TaISLab/Dummy-Arm/CAD/joint3A2.SLDPRT

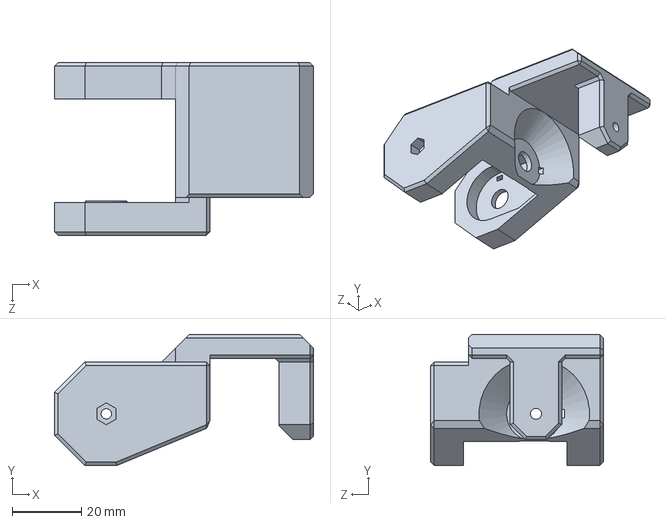
[picture p21: CAD file, 2023-08-25]
CAD/joint3A2.SLDPRT
75.0 x 38.0 x 50.0 mm
