TaISLab/Dummy-Arm/CAD/humero3.SLDPRT

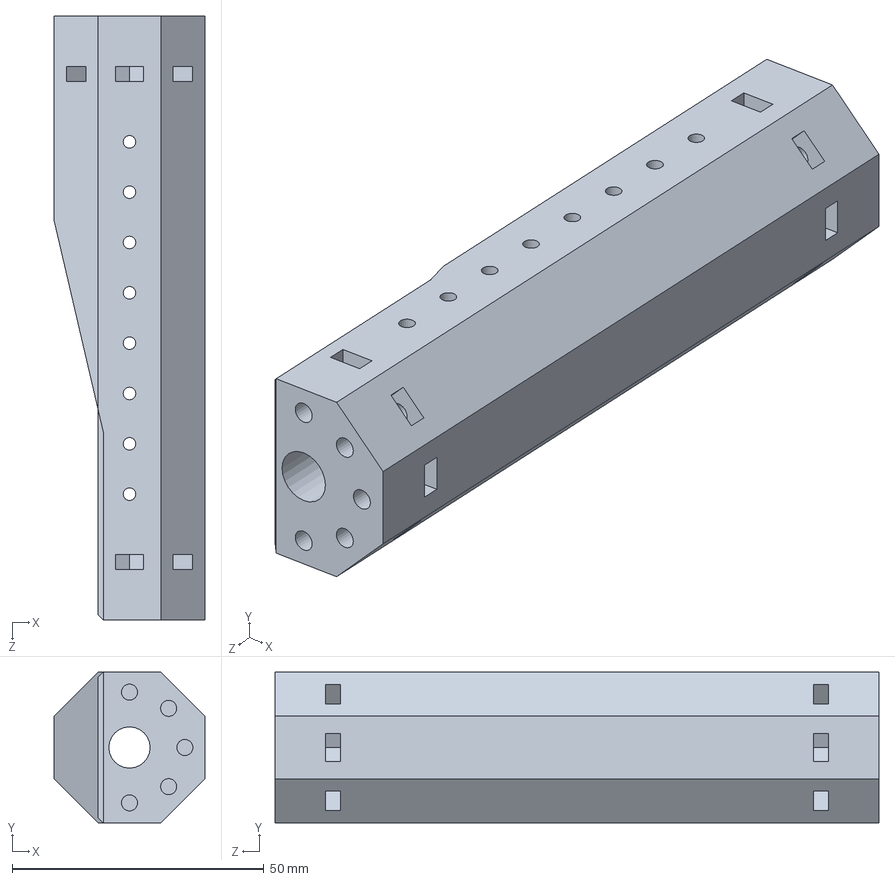
[picture p22: CAD file, 2023-08-25]
CAD/humero3.SLDPRT
30.0 x 30.0 x 120.0 mm
