TaISLab/Dummy-Arm/CAD/jointB.SLDPRT

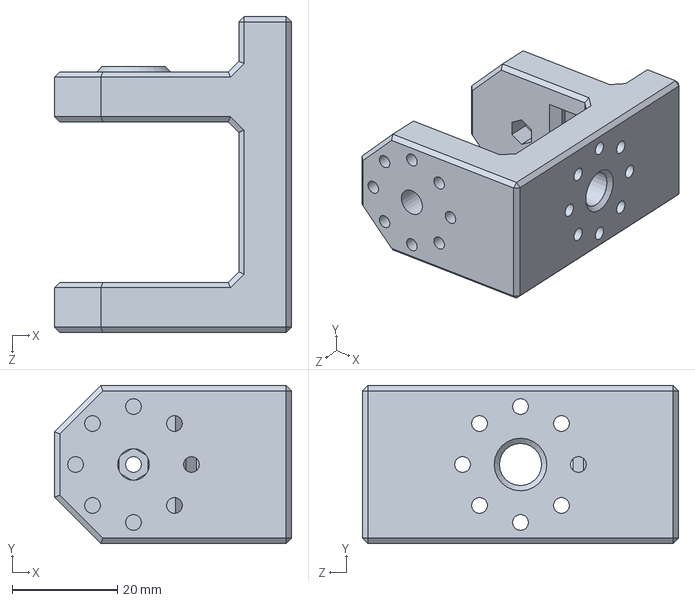
[picture p23: CAD file, 2023-08-25]
CAD/jointB.SLDPRT
45.0 x 30.0 x 60.0 mm
