TaISLab/Dummy-Arm/CAD/wrist.SLDPRT

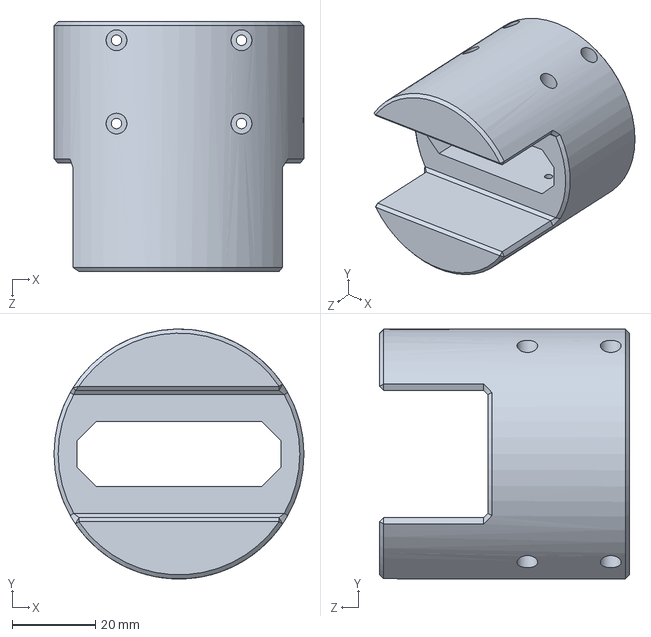
[picture p24: CAD file, 2023-08-25]
CAD/wrist.SLDPRT
60.0 x 60.0 x 60.0 mm
