TaISLab/Dummy-Arm/CAD/radius-ulna3.SLDPRT

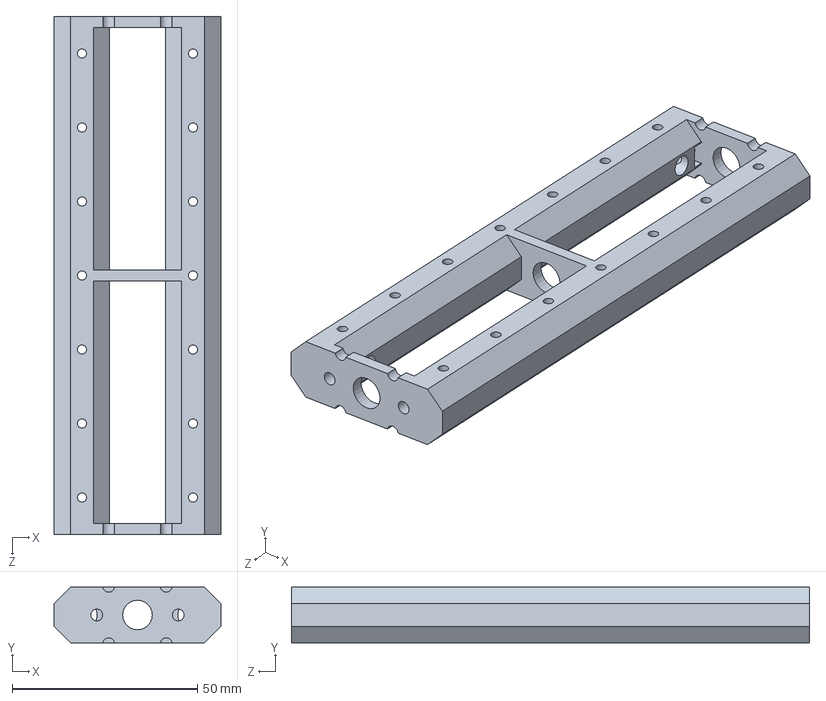
[picture p25: CAD file, 2023-08-25]
CAD/radius-ulna3.SLDPRT
45.0 x 15.0 x 140.0 mm
