TaISLab/Dummy-Arm/CAD/jointA.SLDPRT

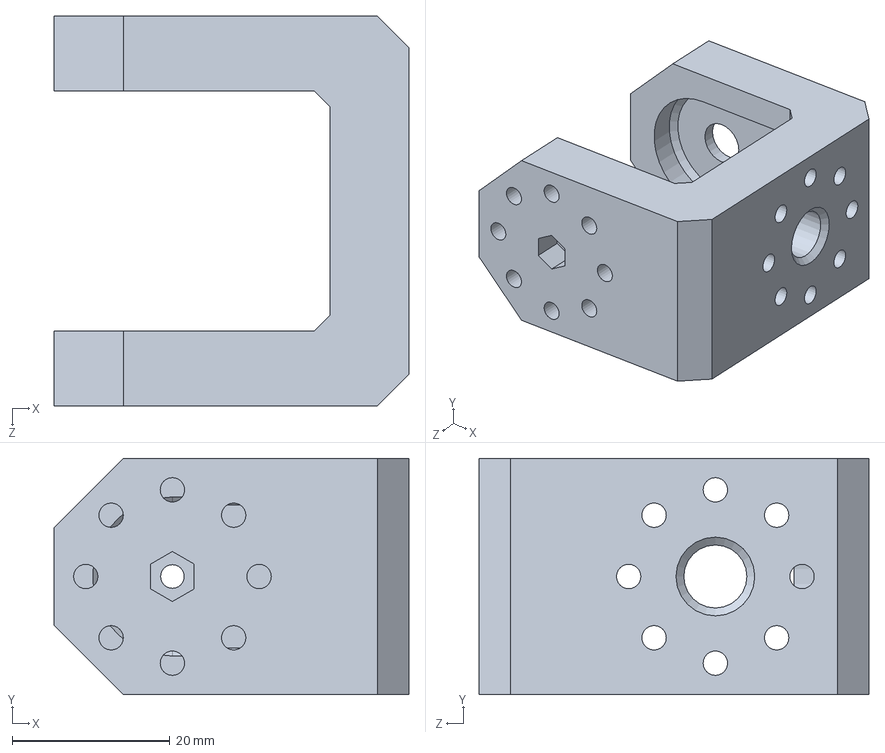
[picture p26: CAD file, 2023-08-25]
CAD/jointA.SLDPRT
45.0 x 30.0 x 49.5 mm
