TaISLab/Dummy-Arm/CAD/humeroB.SLDPRT

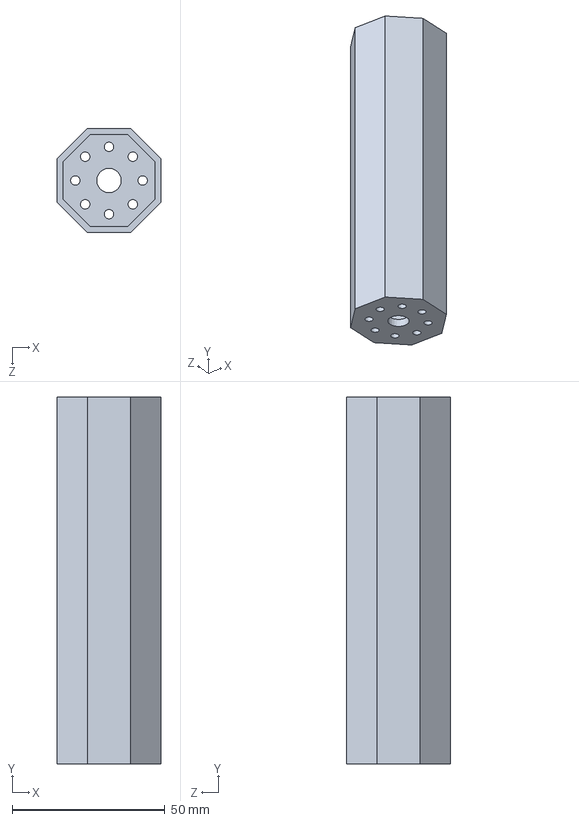
[picture p27: CAD file, 2023-08-24]
CAD/humeroB.SLDPRT
34.0 x 120.0 x 34.0 mm
