TaISLab/Dummy-Arm/CAD/humeroXA.SLDPRT

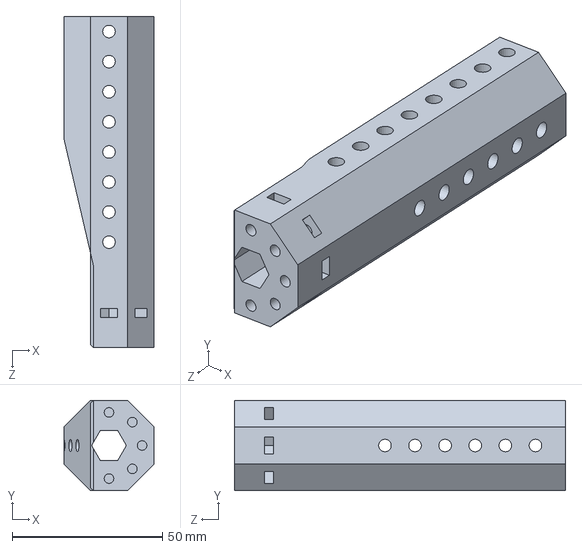
[picture p28: CAD file, 2023-08-24]
CAD/humeroXA.SLDPRT
30.0 x 30.0 x 110.0 mm
