TaISLab/Dummy-Arm/CAD/humero2.SLDPRT

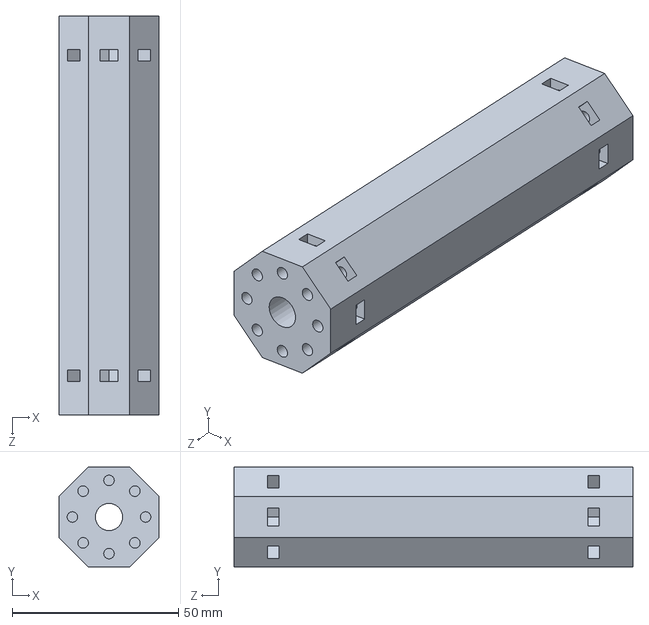
[picture p29: CAD file, 2023-08-24]
CAD/humero2.SLDPRT
30.0 x 30.0 x 120.0 mm
