TaISLab/Dummy-Arm/CAD/humeroA.SLDPRT

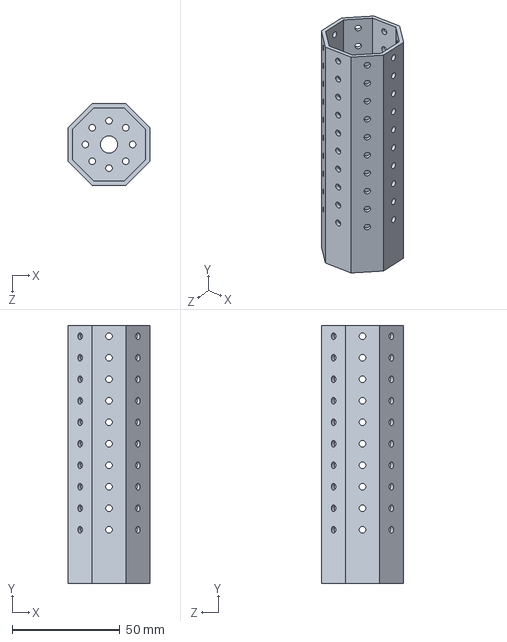
[picture p30: CAD file, 2023-08-24]
CAD/humeroA.SLDPRT
38.0 x 120.0 x 38.0 mm
