TaISLab/Dummy-Arm/CAD/jointC2.SLDPRT

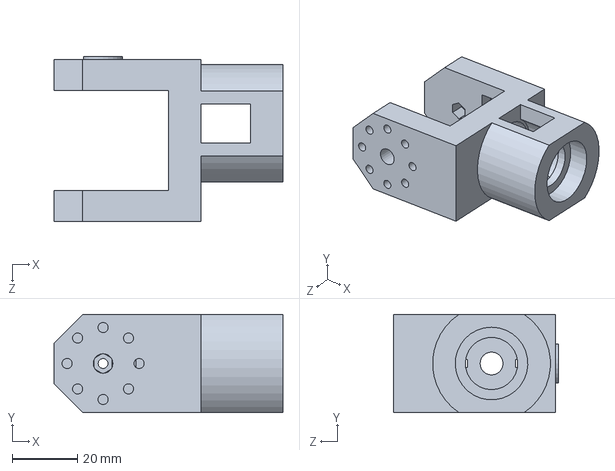
[picture p31: CAD file, 2023-08-24]
CAD/jointC2.SLDPRT
70.0 x 30.0 x 50.5 mm
