TaISLab/Dummy-Arm/CAD/Soporte.SLDPRT

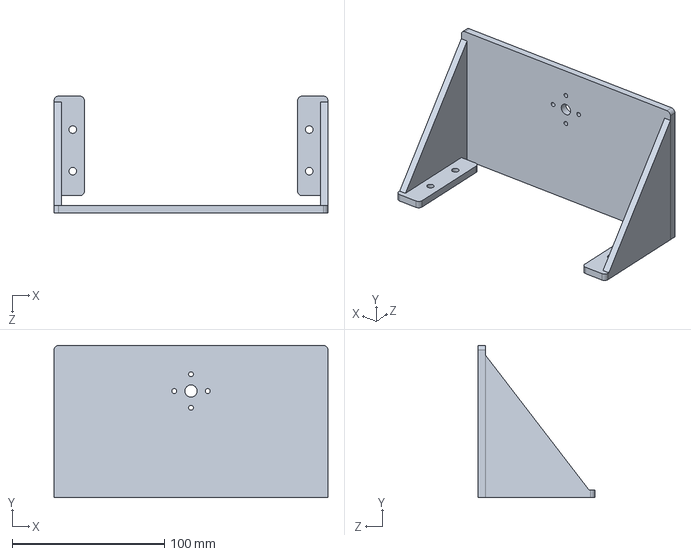
[picture p32: CAD file, 2023-08-24]
CAD/Soporte.SLDPRT
180.0 x 100.0 x 76.7 mm
