TaISLab/Dummy-Arm/CAD/joint3A.SLDPRT

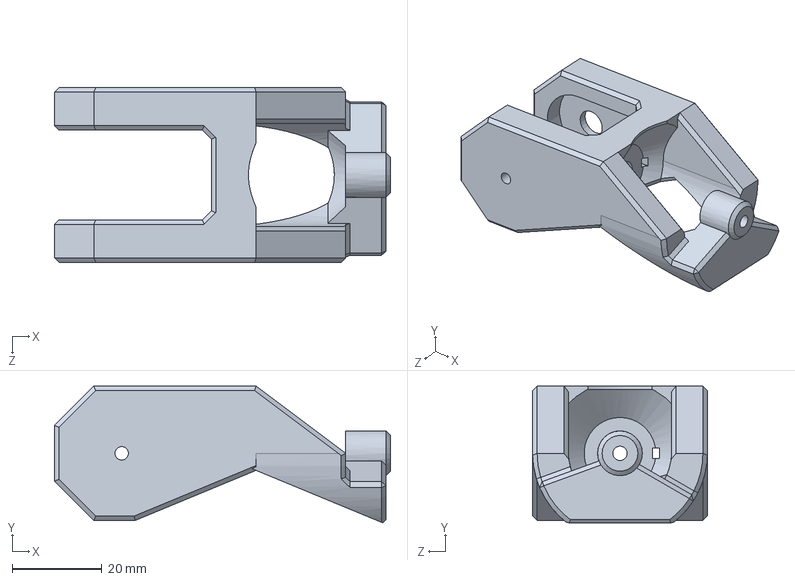
[picture p33: CAD file, 2023-08-24]
CAD/joint3A.SLDPRT
75.0 x 30.5 x 39.0 mm
