TaISLab/Dummy-Arm/CAD/radius-ulna2.SLDPRT

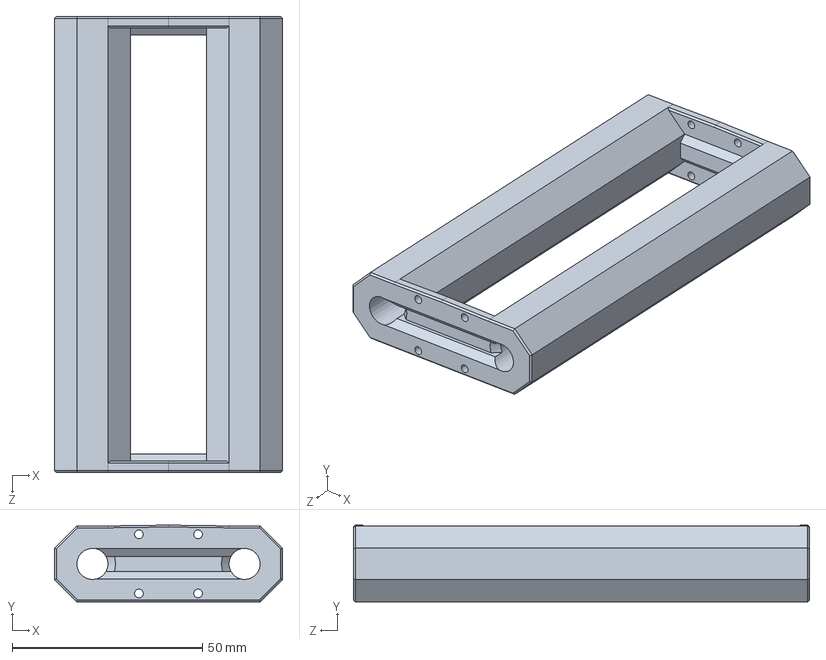
[picture p34: CAD file, 2023-08-24]
CAD/radius-ulna2.SLDPRT
60.0 x 20.2 x 120.0 mm
