TaISLab/Dummy-Arm/CAD/humeroXB.SLDPRT

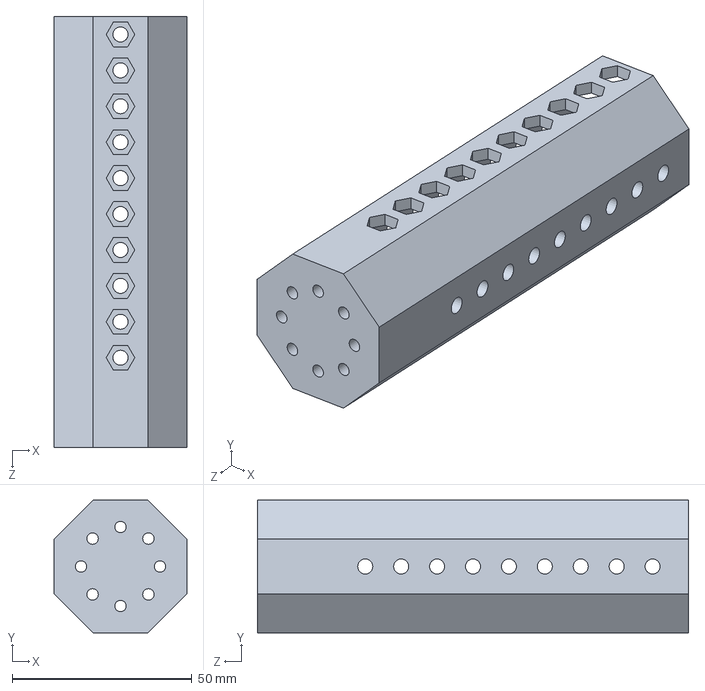
[picture p35: CAD file, 2023-08-24]
CAD/humeroXB.SLDPRT
37.0 x 37.0 x 120.0 mm
