TaISLab/Dummy-Arm/CAD/suplemento-humero3.SLDPRT

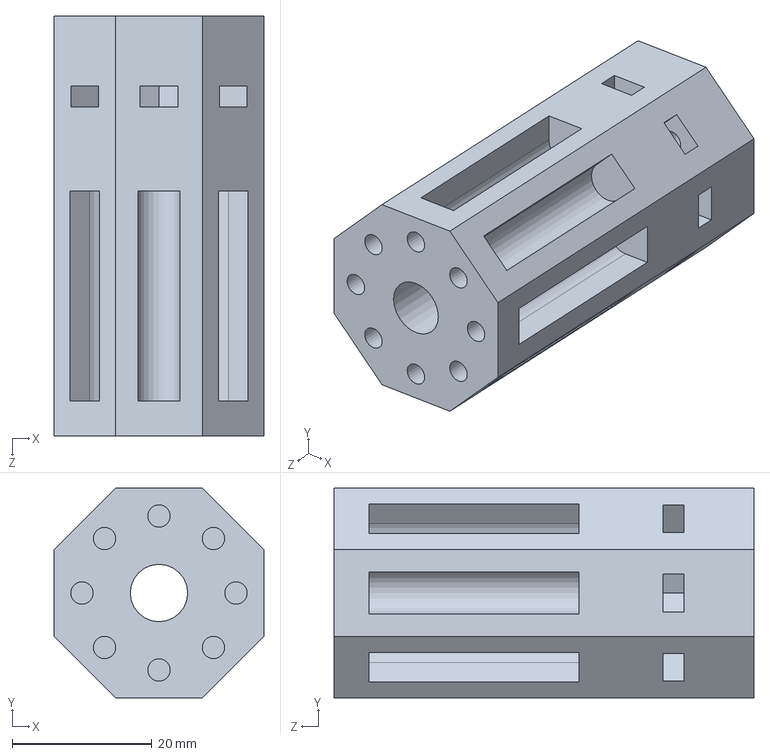
[picture p36: CAD file, 2023-08-24]
CAD/suplemento-humero3.SLDPRT
30.0 x 30.0 x 60.0 mm
